sparkfun/Pro_Micro/Firmware/Example_2a_SimpleKeyboard_HID/Example_2a_SimpleKeyboard_HID.ino

/* HID KeyBoard Example
   by: Jim Lindblom
   date: 1/12/2012
   license: MIT License - Feel free to use this code for any purpose.
   No restrictions. Just keep this license if you go on to use this
   code in your future endeavors! Reuse and share.

   This is very simplistic code that allows you to send a 'z' with
   a momentary pushbutton.
*/

#include <Keyboard.h>
int buttonPin = 9;  // Set a button to any pin

void setup()
{
  pinMode(buttonPin, INPUT);  // Set the button as an input
  digitalWrite(buttonPin, HIGH);  // Pull the button high

  Keyboard.begin(); //Init keyboard emulation
}

void loop()
{
  if (digitalRead(buttonPin) == 0)  // if the button goes low
  {
    Keyboard.write('z');  // send a 'z' to the computer via Keyboard HID
    delay(1000);  // delay so there aren't a kajillion z's
  }
}
